twlennertz/LogicTiles/non-code_project_files/Design Diagrams/3D tile design pics/Horizontal.PNG

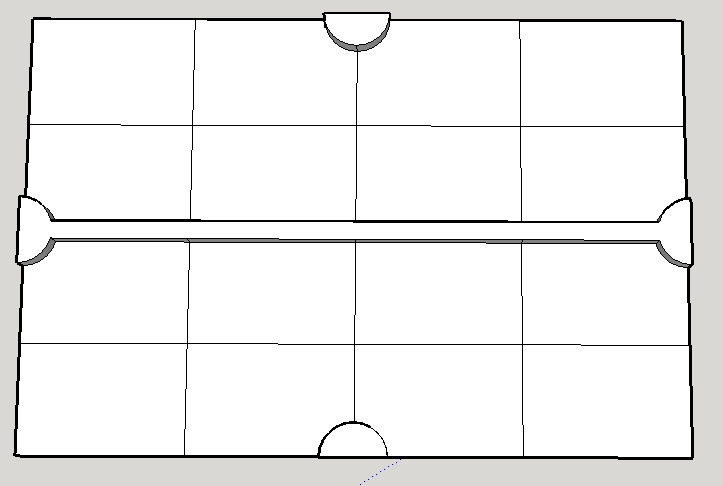
non-code_project_files/Design Diagrams/3D tile design pics/Horizontal.PNG
