twlennertz/LogicTiles/non-code_project_files/Design Diagrams/3D tile design pics/Jump.PNG

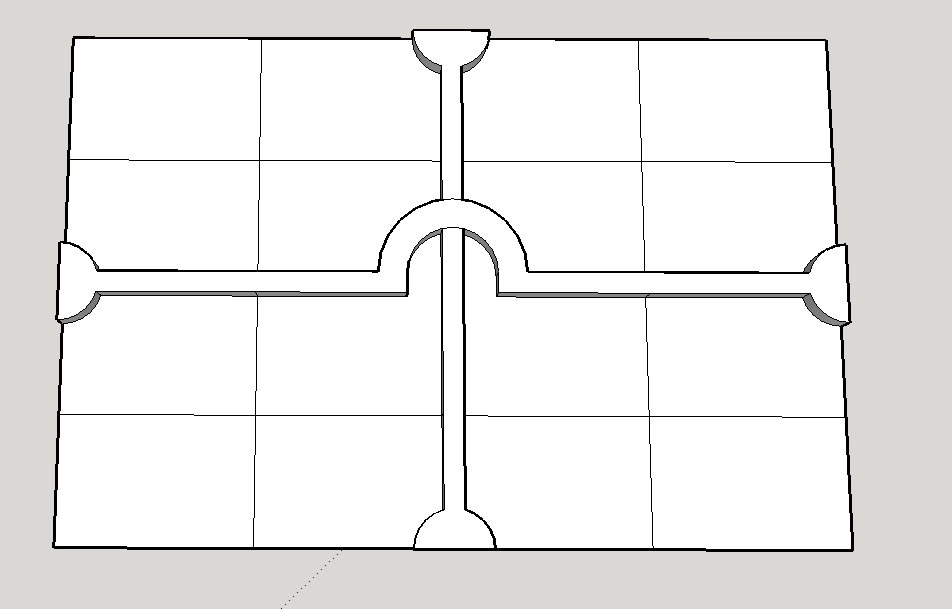
non-code_project_files/Design Diagrams/3D tile design pics/Jump.PNG
