twlennertz/LogicTiles/non-code_project_files/Design Diagrams/3D tile design pics/OR.PNG

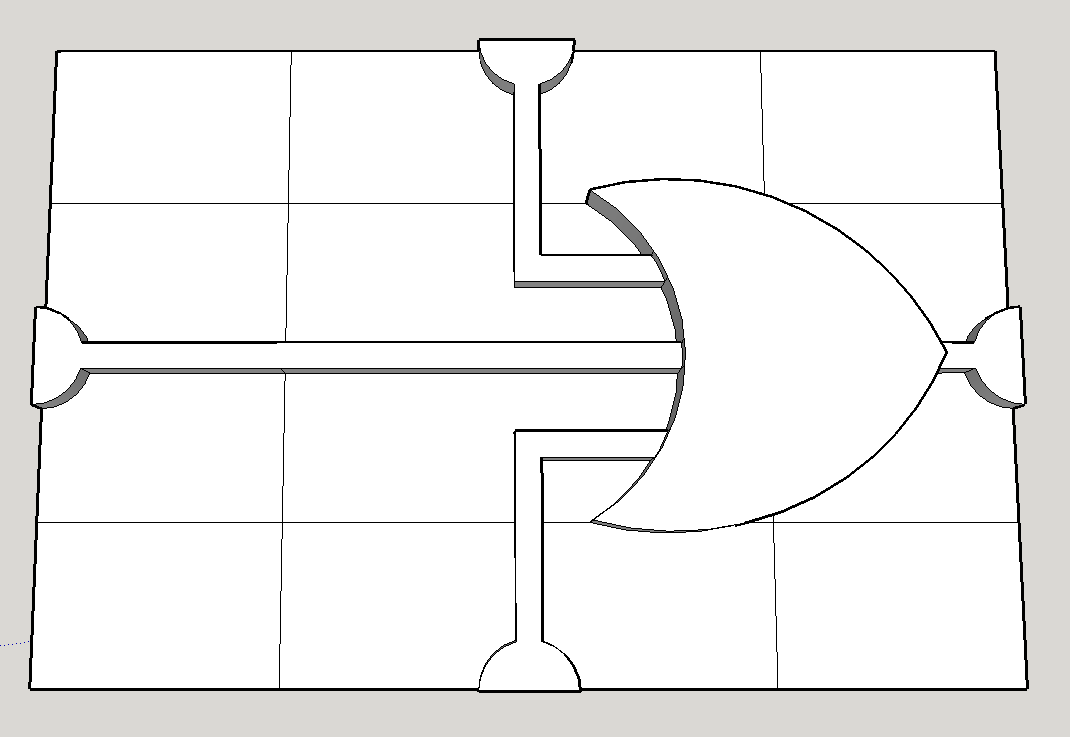
non-code_project_files/Design Diagrams/3D tile design pics/OR.PNG
