twlennertz/LogicTiles/non-code_project_files/Design Diagrams/3D tile design pics/Wire_6_9_12.PNG

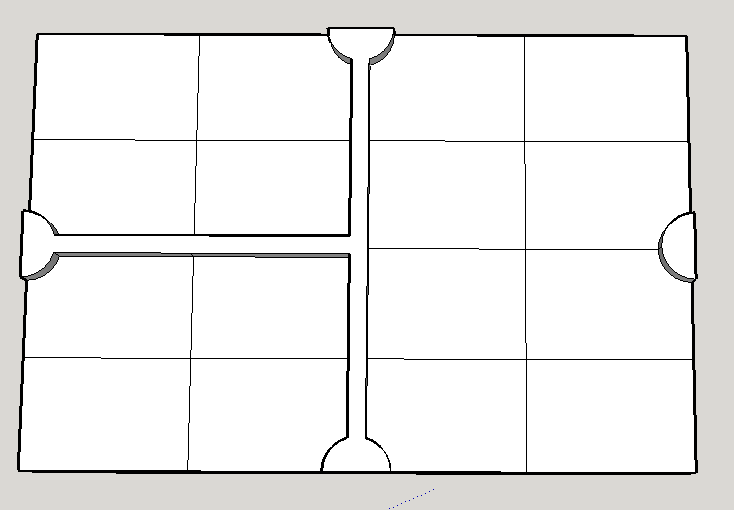
non-code_project_files/Design Diagrams/3D tile design pics/Wire_6_9_12.PNG
