twlennertz/LogicTiles/non-code_project_files/Design Diagrams/3D tile design pics/Wire_9_12_3.PNG

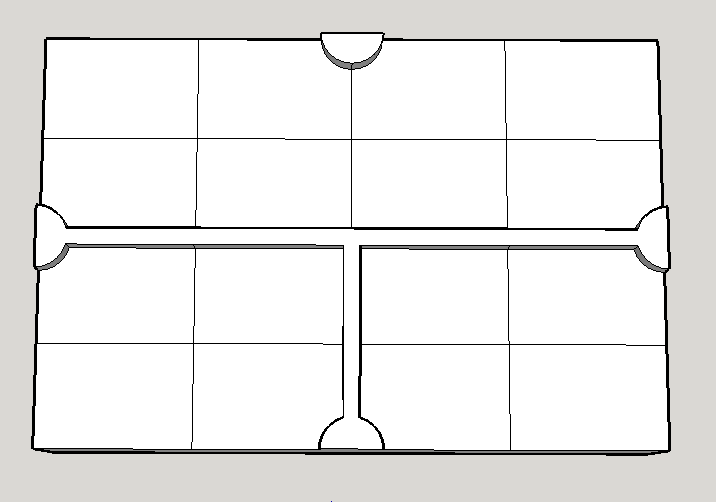
non-code_project_files/Design Diagrams/3D tile design pics/Wire_9_12_3.PNG
