twlennertz/LogicTiles/non-code_project_files/Design Diagrams/3D tile design pics/Wire_12_3_Double.PNG

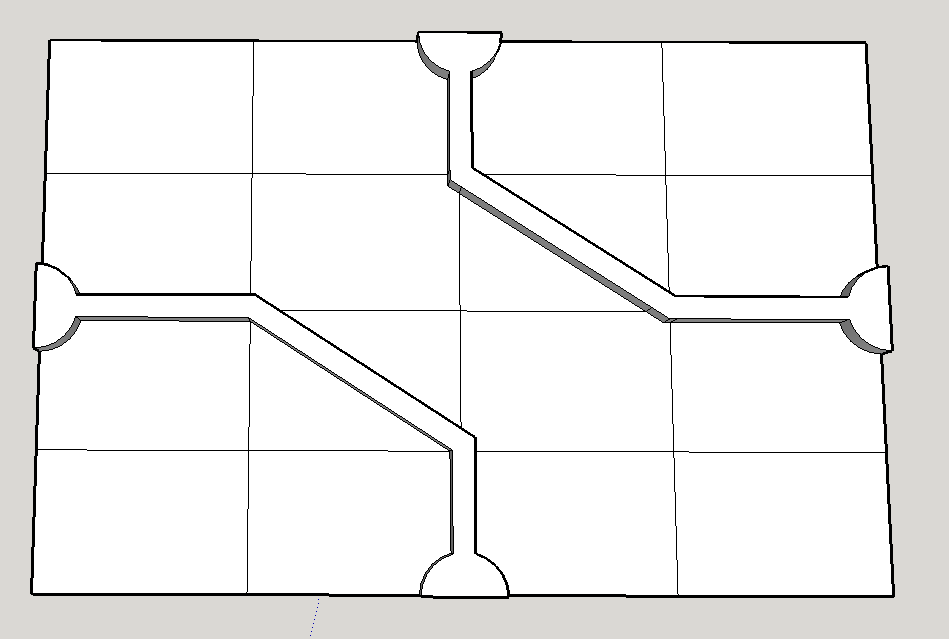
non-code_project_files/Design Diagrams/3D tile design pics/Wire_12_3_Double.PNG
