twlennertz/LogicTiles/non-code_project_files/Design Diagrams/cluster.PNG

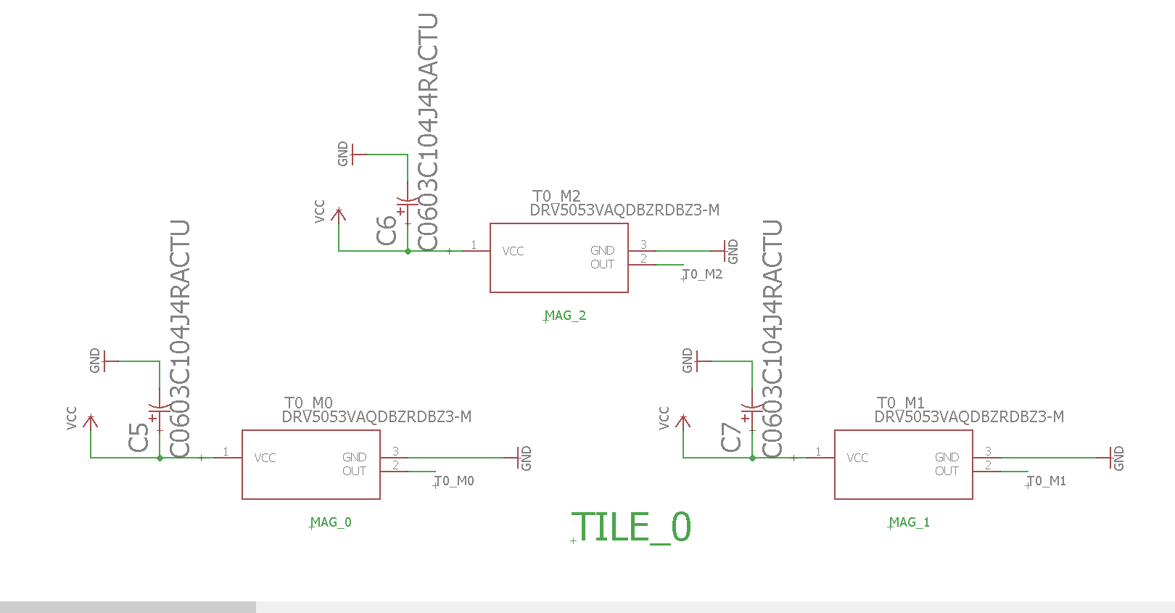
non-code_project_files/Design Diagrams/cluster.PNG
