twlennertz/LogicTiles/non-code_project_files/Design Diagrams/Tile_Dimensions.jpg

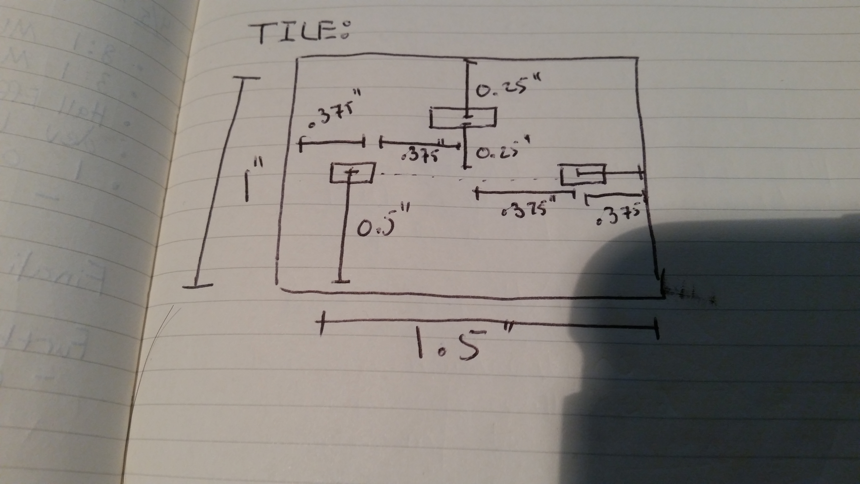
non-code_project_files/Design Diagrams/Tile_Dimensions.jpg
