twlennertz/LogicTiles/non-code_project_files/General Documents/our_board_back.jpg

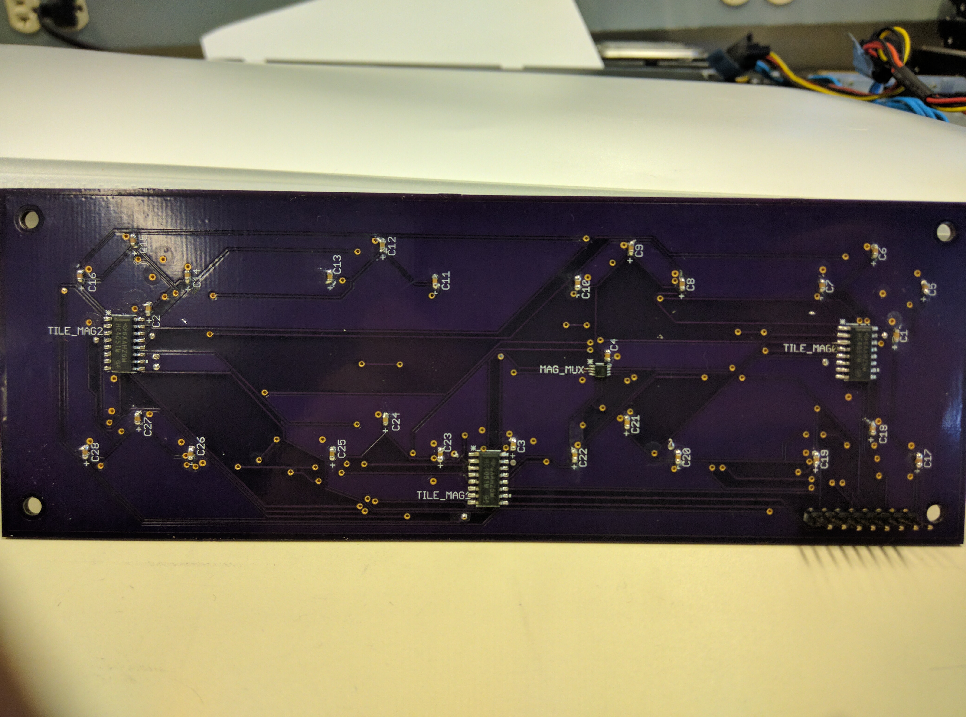
non-code_project_files/General Documents/our_board_back.jpg
