twlennertz/LogicTiles/non-code_project_files/General Documents/our_board_front.jpg

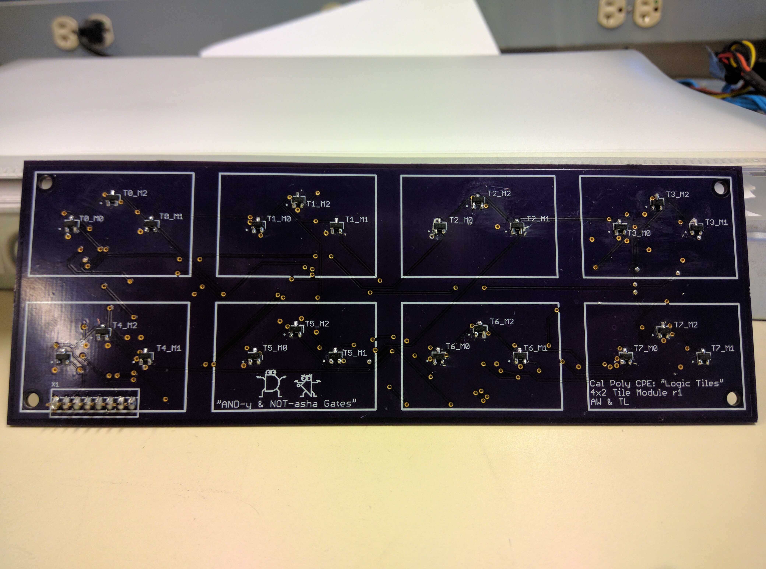
non-code_project_files/General Documents/our_board_front.jpg
