twlennertz/LogicTiles/non-code_project_files/General Documents/PrintTiles_Example.PNG

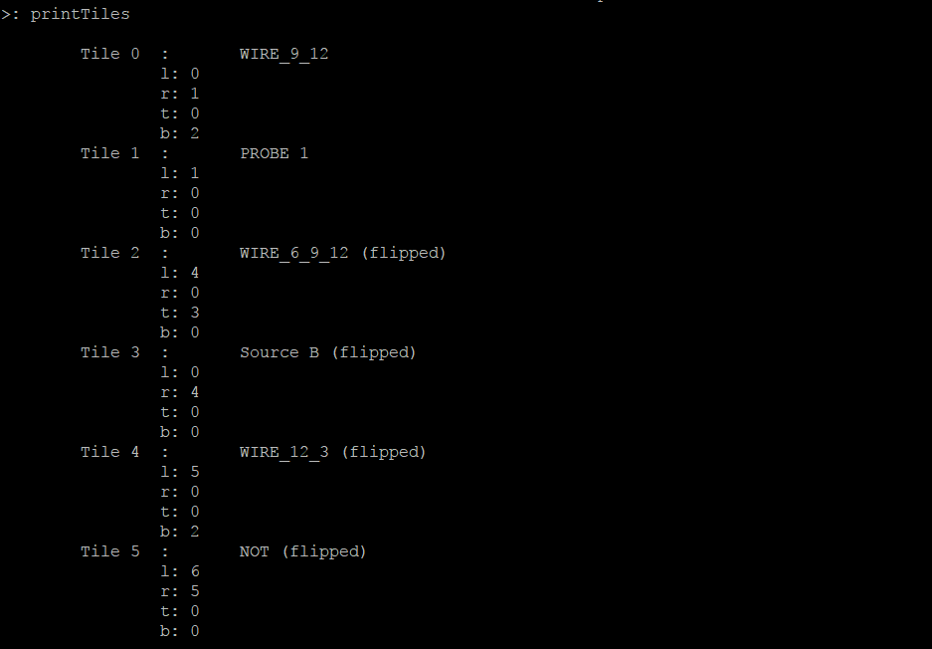
non-code_project_files/General Documents/PrintTiles_Example.PNG
