twlennertz/LogicTiles/graph.h

/* MSP430 Logic Tiles Project - graph.h
 *
 * Authors: Tristan Lennertz & Andrew Wheeler
 */

#ifndef GRAPH_H_
#define GRAPH_H_

typedef struct Node {
    /* Two tiles the node is bridging */
    TileState *tile1;
    TileState *tile2;

    uint8_t visited;                        //for recursive graph traversal
    digiVal value;                          //also for graph traversal
    struct Node *next;                      //for use in the free list

    int id;                                 //for indentifying during debugging
} Node;

digiVal getNodeValue(Node *currNode, TileState *currTile);

digiVal Operation_AND(digiVal v1, digiVal v2, digiVal v3);
digiVal Operation_OR(digiVal v1, digiVal v2, digiVal v3);
digiVal Operation_XOR(digiVal v1, digiVal v2, digiVal v3);
digiVal Operation_NOT(digiVal v);
digiVal Operation_ULTRA(digiVal v1, digiVal v2, digiVal v3, Node *n1, Node *n2, Node *n3);
digiVal Operation_TRI_WIRE(digiVal v1, digiVal v2, Node *n1, Node *n2);

int isGateOutput (Node *node, TileState *tile);
TileState *getOtherTile(Node *node, TileState *tile);
void unvisitAllNodes(TileState *list);

void insertTile(unsigned int changedTile, TileState *tileStates);
void initNodes();
Node *newNode();
void freeNode(Node *toFree);

void leftConfig(TileState *toInsert, TileState *leftTile);
void rightConfig(TileState *toInsert, TileState *rightTile);
void topConfig(TileState *toInsert, TileState *topTile);
void bottomConfig(TileState *toInsert, TileState *bottomTile);

/*Add tile functions*/
void removeTile(TileState *toRemove, TileState *leftTile, TileState *rightTile, TileState *topTile, TileState *bottomTile);

void addGATE(TileState *toInsert, TileState *leftTile, TileState *rightTile, TileState *topTile, TileState *bottomTile);
void addNOT(TileState *toInsert, TileState *leftTile, TileState *rightTile, TileState *topTile, TileState *bottomTile);
void addSOURCE(TileState *toInsert, TileState *leftTile, TileState *rightTile, TileState *topTile, TileState *bottomTile);
void addPROBE(TileState *toInsert, TileState *leftTile, TileState *rightTile, TileState *topTile, TileState *bottomTile);
void addHORIZONTAL(TileState *toInsert, TileState *leftTile, TileState *rightTile, TileState *topTile, TileState *bottomTile);
void addVERTICAL(TileState *toInsert, TileState *leftTile, TileState *rightTile, TileState *topTile, TileState *bottomTile);
void addWIRE_9_12(TileState *toInsert, TileState *leftTile, TileState *rightTile, TileState *topTile, TileState *bottomTile);
void addWIRE_12_3(TileState *toInsert, TileState *leftTile, TileState *rightTile, TileState *topTile, TileState *bottomTile);
void addJUMP(TileState *toInsert, TileState *leftTile, TileState *rightTile, TileState *topTile, TileState *bottomTile);
void addULTRA_NODE(TileState *toInsert, TileState *leftTile, TileState *rightTile, TileState *topTile, TileState *bottomTile);
void addWIRE_9_12_3(TileState *toInsert, TileState *leftTile, TileState *rightTile, TileState *topTile, TileState *bottomTile);
void addWIRE_6_9_12(TileState *toInsert, TileState *leftTile, TileState *rightTile, TileState *topTile, TileState *bottomTile);
void addWIRE_9_12_DOUBLE(TileState *toInsert, TileState *leftTile, TileState *rightTile, TileState *topTile, TileState *bottomTile);
void addWIRE_12_3_DOUBLE(TileState *toInsert, TileState *leftTile, TileState *rightTile, TileState *topTile, TileState *bottomTile);

#endif /* GRAPH_H_ */
