twlennertz/LogicTiles/non-code_project_files/Design Diagrams/triangles.jpg

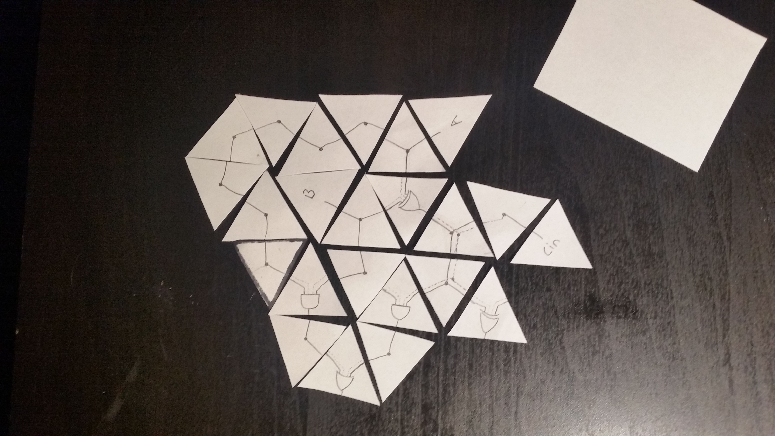
non-code_project_files/Design Diagrams/triangles.jpg
